stivcen01/NesCat1.0_ESP32/EXAMPLES/_Oscilloscope/oscilloscope_screen.png

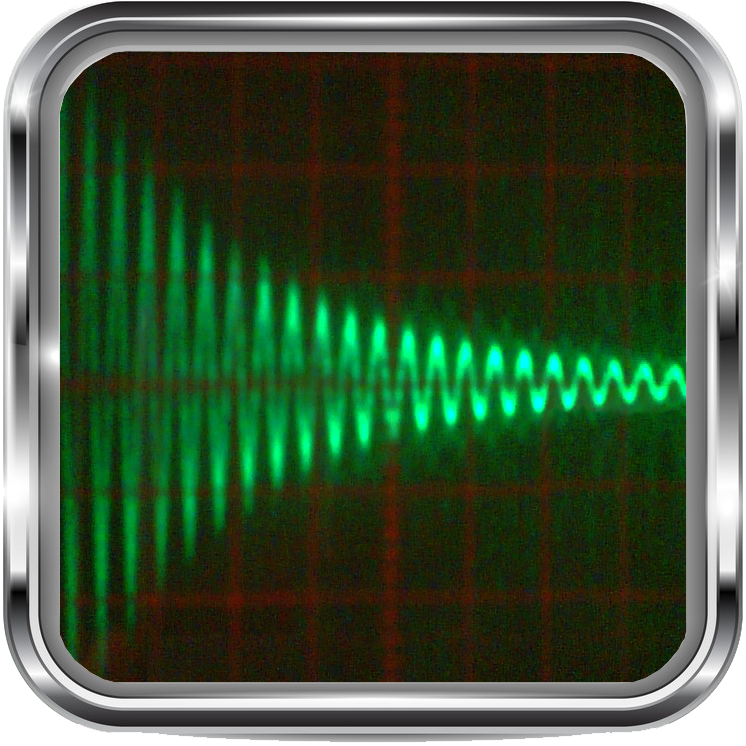
EXAMPLES/_Oscilloscope/oscilloscope_screen.png
