stivcen01/NesCat1.0_ESP32/EXAMPLES/_Player/NCX-PLAYER.png

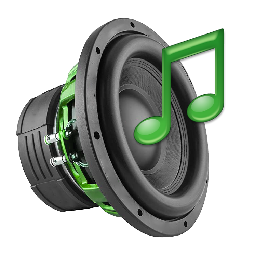
EXAMPLES/_Player/NCX-PLAYER.png
