stivcen01/NesCat1.0_ESP32/HARDWARE/PCB NESCAT 1.0/NESCAT1.0_BRD_TOP.png

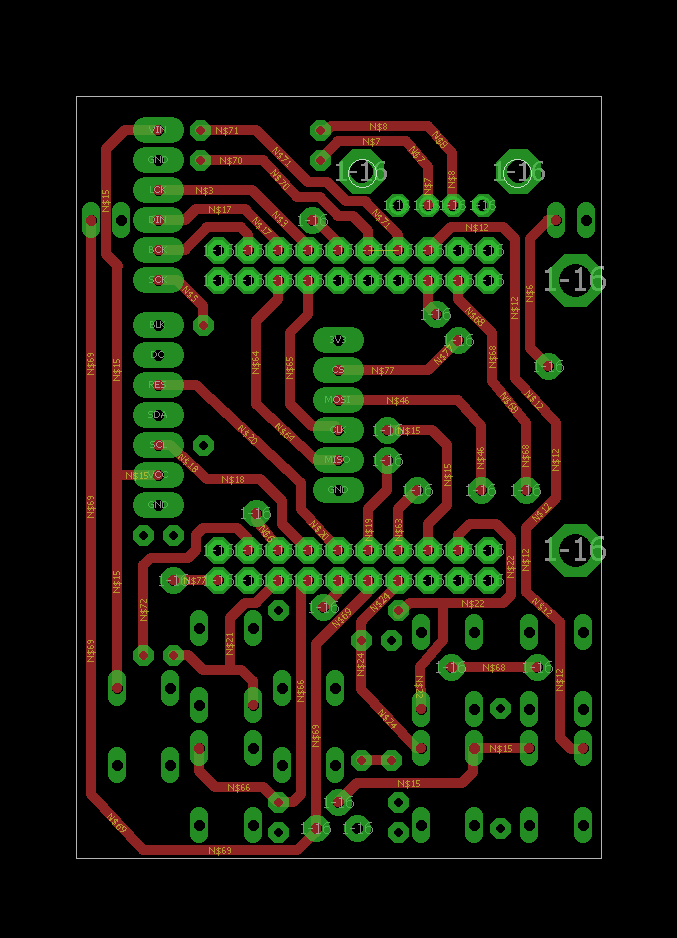
HARDWARE/PCB NESCAT 1.0/NESCAT1.0_BRD_TOP.png
