stivcen01/NesCat1.0_ESP32/RESOURCES/10PCS-LOT-Micro-SD-Storage-Expansion-Board-Mini-Micro-SD-TF-Card-Memory-Shield-Module-With.jpg_Q90.jpg_ (2).jpg

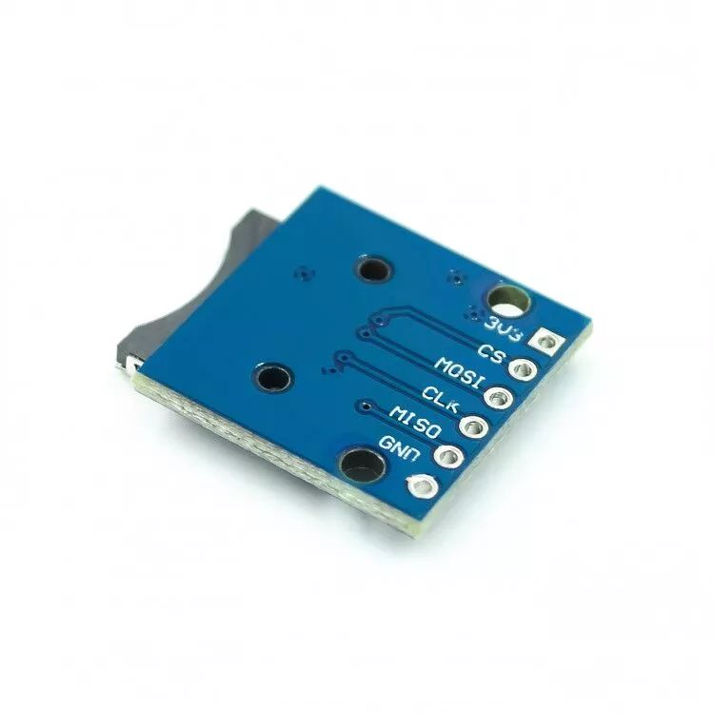
RESOURCES/10PCS-LOT-Micro-SD-Storage-Expansion-Board-Mini-Micro-SD-TF-Card-Memory-Shield-Module-With.jpg_Q90.jpg_ (2).jpg
