stivcen01/NesCat1.0_ESP32/RESOURCES/Interface-I2S-PCM5102A-DAC-Decoder-GY-PCM5102-I2S-Player-Module-For-Raspberry-Pi-pHAT-Format-Board.jpg_Q90.jpg_.jpg

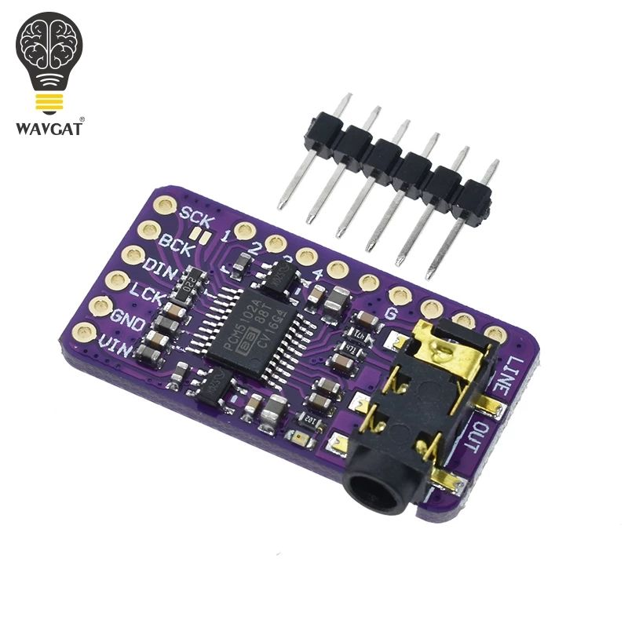
RESOURCES/Interface-I2S-PCM5102A-DAC-Decoder-GY-PCM5102-I2S-Player-Module-For-Raspberry-Pi-pHAT-Format-Board.jpg_Q90.jpg_.jpg
