stivcen01/NesCat1.0_ESP32/oscilloscope.h

#if COMPOSITE_VIDEO_ENABLED

//------------------------
///uint16_t i2s_buff[BUFF_SIZE]; ///using DMA BUFFER 50*1000 samples
uint8_t digital_wave_option = 0; //0-auto | 1-analog | 2-digital data (SERIAL/SPI/I2C/etc)
//------------------------
float v_offset = 0; /// vertical offset is zero in VOLTS
float v_div = 412.5;  ///0.825V/div 4divs!!! -> converted to 8divs (0.412.5V/div)
float v_scale = 0.833333333; //scale 83.3333% verticaly
float h_scale = 0.833333333; //scale 83.3333% horizontaly

uint32_t TIMEBASE = 2; /// 2us or more
//--------------------------------------------------------------------------------
//********************************************************************************
//*  OSCILLOSCOPE FUNCTIONS:                                                     *
//********************************************************************************
class mean_filter {
  public:
    mean_filter(int values) {
      _values = values;
    }

    void init(float value) {
      for (int i = 0; i < _values; i++) {
        _data[i] = value;
      }
    }
    float filter(float reading) {
      float temp = 0;
      _data[_values - 1] = reading;
      for (int i = 0; i < _values - 1; i++) {
        temp += _data[i];
        _data[i] = _data[i + 1];
      }
      temp += reading;
      return temp / float(_values);
    }
    int _values = 5;
    float _data[100] = {0};
};
//--------------------------------------------------------------------------------
float to_scale(float reading) {
  float temp = ///reading-24576;
    TFT_HEIGHT -
    (
      (
        (
          (float)((reading - 24576.0) / 4095.0)
          + (float)(v_offset / 3.3) /// vertical offset is zero in VOLTS
        ) * 3300 /
        (float)(v_div * 8) /// vertically 8divs
      )
    ) * (TFT_HEIGHT - 1) - 1;
  temp = temp * (float)(v_scale); ///vertical scale to %
  temp = temp + (float)(TFT_HEIGHT * ((1 - v_scale) / 2)); // vertical offset from scale/2 %
  return temp;
}
//--------------------------------------------------------------------------------
float to_voltage(float reading) {
  return  (reading - 24576.0) / 4095.0 * 3.3;
}
//--------------------------------------------------------------------------------
//********************************************************************************
void draw_grid() {
  float px_v_per_div = (float)( TFT_HEIGHT * (float)(v_scale)) / 8;
  float px_v_offset = (float)(TFT_HEIGHT * ((1 - v_scale) / 2)); // vertical offset from scale/2 %
  float px_h_per_div = (float)( TFT_WIDTH * (float)(h_scale)) / 8;
  float px_h_offset = (float)(TFT_WIDTH * ((1 - h_scale) / 2)); // vertical offset from scale/2 %

  for (int y = 0; y <= 8; y++) { // 8 divs
    for (int x = 0; x <= 8; x++) { // 8 divs
      //horizontal lines
      if (x < 8)
        for (int i = 0; i < px_h_per_div; i++)  {
          if (i % 8 == 0) screenmemory_drawpixel(x * px_h_per_div + i + px_v_offset, y * px_v_per_div +  px_h_offset , 0x30);
        }
      if (y < 8)
        //vertical lines
        for (int j = 0; j < px_v_per_div; j++)  {
          if (j % 8 == 0) screenmemory_drawpixel(x * px_h_per_div + px_v_offset, y * px_v_per_div + j +  px_h_offset  , 0x30);
        }
    }
  }

  //draw horizontal center line:
  screenmemory_line(px_h_offset , TFT_HEIGHT / 2, TFT_WIDTH - px_h_offset, TFT_HEIGHT / 2, 0x30);

  //draw vertical center line:
  screenmemory_line(TFT_WIDTH / 2 , px_v_offset, TFT_WIDTH / 2, TFT_HEIGHT - px_v_offset, 0x30);
}
//--------------------------------------------------------------------------------
//--------------------------------------------------------------------------------
void peak_mean(uint32_t len, float * max_value, float * min_value, float *pt_mean) {
  max_value[0] = (uint16_t)dma_buff[0][0];
  min_value[0] = (uint16_t)dma_buff[0][0];
  mean_filter filter(5);
  filter.init(dma_buff[0][0]);

  float mean = 0;
  for (uint32_t i = 1; i < len; i++) {
    float value = filter.filter((float)((uint16_t)dma_buff[i / NUM_SAMPLES][i % NUM_SAMPLES]));

    if (value == 0) continue; ///Fix zero values

    if (value > max_value[0]) max_value[0] = value;
    if (value < min_value[0]) min_value[0] = value;

    mean += (uint16_t)dma_buff[i / NUM_SAMPLES][i % NUM_SAMPLES];
  }
  mean /= float(BUFF_SIZE);
  mean = to_voltage(mean);
  pt_mean[0] = mean;
}
//--------------------------------------------------------------------------------
//true if digital/ false if analog
bool digital_analog(uint32_t max_v, uint32_t min_v) {
  uint32_t upper_threshold = max_v - 0.05 * (max_v - min_v);
  uint32_t lower_threshold = min_v + 0.05 * (max_v - min_v);
  uint32_t digital_data = 0;
  uint32_t analog_data = 0;
  for (uint32_t i = 0; i < BUFF_SIZE; i++) {
    if (dma_buff[i / NUM_SAMPLES][i % NUM_SAMPLES] > lower_threshold) {
      if (dma_buff[i / NUM_SAMPLES][i % NUM_SAMPLES] > upper_threshold) {
        //HIGH DIGITAL
        digital_data++;
      } else {
        //ANALOG/TRANSITION
        analog_data++;
      }
    } else {
      //LOW DIGITAL
      digital_data++;
    }
  }
  //more than 50% of data is analog
  if (analog_data < digital_data) return true;
  return false;
}
//--------------------------------------------------------------------------------
void trigger_freq_analog(float sample_rate,
                         float mean,
                         uint32_t max_v,
                         uint32_t min_v,
                         float *pt_freq,
                         float *pt_period,
                         uint32_t *pt_trigger0,
                         uint32_t *pt_trigger1) {
  float freq = 0;
  float period = 0;
  bool signal_side = false;
  uint32_t trigger_count = 0;
  uint32_t trigger_num = 10;
  uint32_t trigger_temp[trigger_num] = {0};
  uint32_t trigger_index = 0;

  //get initial signal relative to the mean
  if (to_voltage(dma_buff[0][0]) > mean) {
    signal_side = true;
  }

  //waveform repetitions calculation + get triggers time
  uint32_t wave_center = (max_v + min_v) / 2;
  for (uint32_t i = 1 ; i < BUFF_SIZE; i++) {
    if (signal_side && dma_buff[i / NUM_SAMPLES][i % NUM_SAMPLES] < wave_center - (wave_center - min_v) * 0.2) {
      signal_side = false;
    } else if (!signal_side && dma_buff[i / NUM_SAMPLES][i % NUM_SAMPLES] > wave_center + (max_v - wave_center) * 0.2) {
      freq++;
      if (trigger_count < trigger_num) {
        trigger_temp[trigger_count] = i;
        trigger_count++;
      }
      signal_side = true;
    }
  }
  //frequency calculation
  if (trigger_count < 2) {
    trigger_temp[0] = 0;
    trigger_index = 0;
    freq = 0;
    period = 0;
  } else {
    //simple frequency calculation fair enough for frequencies over 2khz (20hz resolution)
    freq = freq * NUM_SAMPLES / 50;
    period = (float)(sample_rate * 1000.0) / freq; //us

    //from 2000 to 80 hz -> uses mean of the periods for precision
    /*
          if (freq < 2000 && freq > 80) {
             period = 0;
             for (uint32_t i = 1; i < trigger_count; i++) {
                period += trigger_temp[i] - trigger_temp[i - 1];
             }
             period /= (trigger_count - 1);
             freq = sample_rate * 1000 / period;
          }

          //under 80hz, single period for frequency calculation
          else if (trigger_count > 1 && freq <= 80) {
             period = trigger_temp[1] - trigger_temp[0];
             freq = sample_rate * 1000 / period;
          }
    */
  }

  //setting triggers offset and getting second trigger for debug cursor on drawn_channel1

  ///The trigger function uses a rise porcentage (5%) obove the mean, thus,
  ///the real waveform starting point is some datapoints back.
  ///The resulting trigger gets a negative offset of 5% of the calculated period

  uint32_t trigger2 = 0;
  if (trigger_temp[0] - period * 0.05 > 0 && trigger_count > 1) {
    trigger_index = trigger_temp[0] - period * 0.05;
    trigger2 = trigger_temp[1] - period * 0.05;
  } else if (trigger_count > 2) {
    trigger_index = trigger_temp[1] - period * 0.05;
    if (trigger_count > 2) trigger2 = trigger_temp[2] - period * 0.05;
  }

  pt_trigger0[0] = trigger_index;
  pt_trigger1[0] = trigger2;
  pt_freq[0] = freq;
  pt_period[0] = period;
}
//--------------------------------------------------------------------------------
void trigger_freq_digital(float sample_rate,
                          float mean,
                          uint32_t max_v,
                          uint32_t min_v,
                          float *pt_freq,
                          float *pt_period,
                          uint32_t *pt_trigger0) {

  float freq = 0;
  float period = 0;
  bool signal_side = false;
  uint32_t trigger_count = 0;
  uint32_t trigger_num = 10;
  uint32_t trigger_temp[trigger_num] = {0};
  uint32_t trigger_index = 0;

  //get initial signal relative to the mean
  if (to_voltage(dma_buff[0][0]) > mean) {
    signal_side = true;
  }

  //waveform repetitions calculation + get triggers time
  uint32_t wave_center = (max_v + min_v) / 2;
  bool normal_high = (mean > to_voltage(wave_center)) ? true : false;
  if (max_v - min_v > 4095 * (0.4 / 3.3)) {
    for (uint32_t i = 1 ; i < BUFF_SIZE; i++) {
      if (signal_side && dma_buff[i / NUM_SAMPLES][i % NUM_SAMPLES] < wave_center - (wave_center - min_v) * 0.2) {
        //signal was high, fell -> trigger if normal high
        if (trigger_count < trigger_num && normal_high) {
          trigger_temp[trigger_count] = i;
          trigger_count++;
        }
        signal_side = false;
      } else if (!signal_side && dma_buff[i / NUM_SAMPLES][i % NUM_SAMPLES] > wave_center + (max_v - wave_center) * 0.2) {
        freq++;
        //signal was low, rose -> trigger if normal low
        if (trigger_count < trigger_num && !normal_high) {
          trigger_temp[trigger_count] = i;
          trigger_count++;
        }
        signal_side = true;
      }
    }

    //Digital frequency calculation:
    freq = 281.7133902265831 * freq;
    period = ((float)(sample_rate * 1000.0) / freq) / (28.636 / 2); //us

    if (trigger_count > 1) {
      //from 2000 to 80 hz -> uses mean of the periods for precision
      if (freq < 2000 && freq > 80) {
        period = 0;
        for (uint32_t i = 1; i < trigger_count; i++) {
          period += trigger_temp[i] - trigger_temp[i - 1];
        }
        period /= (trigger_count - 1);
        freq = sample_rate * (NUM_SAMPLES) / period;
      }
      //under 80hz, single period for frequency calculation
      else if (trigger_count > 1 && freq <= 80) {
        period = trigger_temp[1] - trigger_temp[0];
        freq = sample_rate * (2800 / 2) / period;
      }
    }
    trigger_index = trigger_temp[0];

    if (trigger_index > 10) trigger_index -= 10;
    else trigger_index = 0;
  }
  pt_trigger0[0] = trigger_index;
  pt_freq[0] = freq;
  pt_period[0] = period;
}
//********************************************************************************

int shift = 125; //info text shift X
bool info = true;

bool ADC_EXIT = false;
uint8_t spritecolor = 26;

bool timebase_switched=false;


//===============================================================================
void REINIT_ADC(){
  
      // Switch on Slave mode.
      // I2S_CONF_REG -> I2S_RX_SLAVE_MOD
      // Set to 1 to enable slave mode.
      I2S0.conf.rx_slave_mod = 0; //not 1 !!!


      // Enable parallel mode
      // I2S_CONF2_REG -> I2S_LCD_END
      // Set to 1 to enable LCD mode.
      I2S0.conf2.lcd_en = 1;

      // Use HSYNC/VSYNC/HREF to control sampling
      // I2S_CONF2_REG -> I2S_CAMERA_EN
      // Set to 1 to enable camera mode.
      /// I2S0.conf2.camera_en = 1;


      // Configure clock divider
      I2S0.clkm_conf.clkm_div_a   = 1;
      I2S0.clkm_conf.clkm_div_b   = 0;
      I2S0.clkm_conf.clkm_div_num = 1;

      // I2S_FIFO_CONF_REG -> I2S_DSCR_EN
      // FIFO will sink data to DMA
      I2S0.fifo_conf.dscr_en = 1;

      // FIFO configuration
      // I2S_FIFO_CONF_REG -> RX_FIFO_MOD
      I2S0.fifo_conf.rx_fifo_mod          = 1; // 0-3???

      // I2S_FIFO_CONF_REG -> RX_FIFO_MOD_FORCE_EN
      I2S0.fifo_conf.rx_fifo_mod_force_en = 1;

      // I2S_CONF_CHAN_REG -> I2S_RX_CHAN_MOD
      I2S0.conf_chan.rx_chan_mod          = 1;

      // Clear flags which are used in I2S serial mode
      // I2S_SAMPLE_RATE_CONF_REG -> I2S_RX_BITS_MOD
      I2S0.sample_rate_conf.rx_bits_mod = 0;

      // I2S_CONF_REG -> I2S_RX_RIGHT_FIRST
      I2S0.conf.rx_right_first = 0;
      //I2S0.conf.rx_right_first = 0;

      // I2S_CONF_REG -> I2S_RX_MSB_RIGHT
      I2S0.conf.rx_msb_right   = 0;
      //I2S0.conf.rx_msb_right   = 1;

      // I2S_CONF_REG -> I2S_RX_MSB_SHIFT
      I2S0.conf.rx_msb_shift   = 0;
      //I2S0.conf.rx_msb_shift   = 1;

      // I2S_CONF_REG -> I2S_RX_MSB_MONO
      I2S0.conf.rx_mono        = 1;

      // I2S_CONF_REG -> I2S_RX_SHORT_SYNC
      I2S0.conf.rx_short_sync  = 0;

      I2S0.timing.val          = 0;

      for (uint32_t buff_idx = 0; buff_idx < 50; buff_idx++) {
        dma_descriptor[buff_idx].length = 0; //number of byte written to the buffer
        ///    dma_descriptor[buff_idx].size = sizeof(dma_buff[buff_idx]); //max size of the buffer in bytes
        dma_descriptor[buff_idx].size = 2000;  //max size of the buffer in bytes
        dma_descriptor[buff_idx].owner = 1;
        dma_descriptor[buff_idx].sosf = 1;
        dma_descriptor[buff_idx].buf = (uint8_t*)&dma_buff[buff_idx][0];
        dma_descriptor[buff_idx].offset = 0;
        dma_descriptor[buff_idx].empty = 0;
        dma_descriptor[buff_idx].eof = 1;
        //pointer to the next descriptor
        if (buff_idx == 49) dma_descriptor[buff_idx].qe.stqe_next = &dma_descriptor[0];
        else dma_descriptor[buff_idx].qe.stqe_next = &dma_descriptor[buff_idx + 1];
      }
      I2S0.in_link.addr = (uint32_t)&dma_descriptor[0];

      ///Serial.println(dma_descriptor[1].buf[0]);

      // I2S_RX_EOF_NUM_REG
      /// I2S0.rx_eof_num   = sample_count;
      I2S0.rx_eof_num   = 2000 * 50;

      // I2S_IN_LINK_REG -> I2S_INLINK_ADDR
      /// I2S0.in_link.addr = (uint32_t) pFirst;

      // I2S_IN_LINK_REG -> I2S_INLINK_START
      I2S0.in_link.start   = 1;

      // toto sposobuje skakanie obrazu:
      /*  I2S0.int_clr.val   = I2S0.int_raw.val;
        I2S0.int_ena.val   = 0;
        I2S0.int_ena.in_done = 1;
      */
//===============================================================================
}      
//********************************************************************************
//*  ADC TASK:                                                                   *
//********************************************************************************
void core1_task( void * pvParameters ) {
  (void) pvParameters;
  for (;;) {

    float mean = 0;
    float max_v, min_v;
    float freq = 0;
    float period = 0;
    uint32_t trigger0 = 0;
    uint32_t trigger1 = 0;

    float sample_rate = 28636 / 2; // 28.636/2 Mhz

//--------------------------------------------------------------------------------
    //buttons read
    uint32_t lastmtime = millis();
    uint32_t offsetmtime = 250;

    if (TIMEBASE > 1000) offsetmtime = 1000; //1000ms delay
    else offsetmtime = 250; //250ms delay

    while (lastmtime + offsetmtime > millis()) {
      vTaskDelay(pdMS_TO_TICKS(1)); ///1ms delay

      if (digitalRead(PIN_A) == 1) {
        JOY_CROSS = 1;  //A
      }
      if (digitalRead(PIN_B) == 1) {
        JOY_SQUARE = 1;   //B
      }
      if (digitalRead(PIN_SELECT) == 1) {
        JOY_OPTIONS = 1;   //SELECT
      }
      if (digitalRead(PIN_START) == 1) {
        JOY_SHARE = 1;   //START
      }
      if (digitalRead(PIN_UP) == 1) {
        JOY_UP = 1;
      }
      if (digitalRead(PIN_DOWN) == 1) {
        JOY_DOWN = 1;   //DOWN
      }
      if (digitalRead(PIN_LEFT) == 1) {
        JOY_LEFT = 1;   //LEFT
      }
      if (digitalRead(PIN_RIGHT) == 1) {
        JOY_RIGHT = 1;   //RIGHT
      }
    }
//--------------------------------------------------------------------------------

    I2S0.conf.rx_start = 0; /// stop DMA ADC

//--------------------------------------------------------------------------------
    if (JOY_SHARE == 1 && JOY_OPTIONS == 1) { //EXIT
      JOY_SHARE = 0;
      JOY_OPTIONS = 0;
      EXIT = true;
      delay(250);
    }
    if (JOY_CROSS == 1) {  /// PAUSE
      delay(250);
      while (JOY_CROSS == 1) {
        if (digitalRead(PIN_A) == 1) {
          JOY_CROSS = 0;
        }
        delay(10);
      }
    }
    if (JOY_SHARE == 1) {
      if (spritecolor == 26) spritecolor = 6; //green to red
      else if (spritecolor == 6) spritecolor = 1; //red to blue
      else if (spritecolor == 1) spritecolor = 40; //blue to yellow
      else if (spritecolor == 40) spritecolor = 26; //yellow to green
      else spritecolor = 6;
      JOY_SHARE = 0;
    }
    if (JOY_SQUARE == 1) { /// SHOW/HIDE info
      if (digital_wave_option == 0) digital_wave_option = 1;
      else if (digital_wave_option == 1) digital_wave_option = 2;
      else if (digital_wave_option == 2) digital_wave_option = 0;
      else digital_wave_option = 0;
      JOY_SQUARE = 0;
    }
    if (JOY_OPTIONS == 1) { /// SHOW/HIDE info
      if (info == true) info = false;
      else info = true;
      JOY_OPTIONS = 0;
    }
    if (JOY_LEFT == 1) {
      switch (TIMEBASE) {
        case 10000:
          TIMEBASE = 5000;
          break;
        case 5000:
          TIMEBASE = 2000;
          break;
        case 2000:
          TIMEBASE = 1000;
          break;
        case 1000:
          TIMEBASE = 500;
          break;
        case 500:
          TIMEBASE = 200;
          break;
        case 200:
          TIMEBASE = 100;
          break;
        case 100:
          TIMEBASE = 50;
          break;
        case 50:
          TIMEBASE = 20;
          break;
        case 20:
          TIMEBASE = 10;
          break;
        case 10:
          TIMEBASE = 5;
          break;
        case 5:
          TIMEBASE = 2;
          break;
        case 2:
          TIMEBASE = 2; //minimum us/div
          break;
        default:
          TIMEBASE = 10000;
      }
      JOY_LEFT = 0;
      timebase_switched=true;
    }
    if (JOY_RIGHT == 1) {
      switch (TIMEBASE) {
        case 2:
          TIMEBASE = 5;
          break;
        case 5:
          TIMEBASE = 10;
          break;
        case 10:
          TIMEBASE = 20;
          break;
        case 20:
          TIMEBASE = 50;
          break;
        case 50:
          TIMEBASE = 100;
          break;
        case 100:
          TIMEBASE = 200;
          break;
        case 200:
          TIMEBASE = 500;
          break;
        case 500:
          TIMEBASE = 1000;
          break;
        case 1000:
          ///TIMEBASE = 2000;
          TIMEBASE = 1000; //stop here (disabled more than 1ms )
          break;
        case 2000:
          TIMEBASE = 5000;
          break;
        case 5000:
          TIMEBASE = 10000;
          break;
        case 10000:
          TIMEBASE = 10000; //maximum us/div
          break;
        default:
          TIMEBASE = 2;
      }
      JOY_RIGHT = 0;
      timebase_switched=true;
    }


//--------------------------------------------------------------------------------

    peak_mean(BUFF_SIZE, &max_v, &min_v, &mean);

//--------------------------------------------------------------------------------
    //if analog mode OR auto mode and wave recognized as analog

    bool digital_data = false;
    if (digital_wave_option == 1) {
      trigger_freq_analog(sample_rate, mean, max_v, min_v, &freq, &period, &trigger0, &trigger1);
    }  else if (digital_wave_option == 0) {
      digital_data = digital_analog(max_v, min_v);
      if (!digital_data) {
        trigger_freq_analog(sample_rate, mean, max_v, min_v, &freq, &period, &trigger0, &trigger1);
      } else {
        trigger_freq_digital(sample_rate, mean, max_v, min_v, &freq, &period, &trigger0);
      }
    } else {
      trigger_freq_digital(sample_rate, mean, max_v, min_v, &freq, &period, &trigger0);
    }
//--------------------------------------------------------------------------------
    //Clear Screen
    screenmemory_fillscreen(0x3f);

    //Draw Grid
    draw_grid();
//--------------------------------------------------------------------------------
    //DEBUG DATA

    if (DEBUG) {
      Serial.print("digital=1_analog=0: ");
      Serial.println(digital_analog(max_v, min_v));

      Serial.print("mean:");
      Serial.println(mean);
      Serial.print("max_v:");
      Serial.println(max_v);
      Serial.print("min_v:");
      Serial.println(min_v);
      Serial.print("freq:");
      Serial.println(freq);
      Serial.print("period:");
      Serial.println(period);
      Serial.print("trigger0:");
      Serial.println(trigger0);
    }

//--------------------------------------------------------------------------------
    
    ///adjust TIMEBASE:
    if (timebase_switched==true) {
      I2S0.in_link.start   = 0;

    switch (TIMEBASE) {
      case 2:
        rtc_clk_apll_enable(1, 222, 115, 7,0);   //28,636363636 MHz (doubled)   ///tunned maybe ok
        I2S0.sample_rate_conf.tx_bck_div_num = 2;        
        I2S0.sample_rate_conf.rx_bck_div_num = 2; //2x scale time base
        break;
      case 5:
        rtc_clk_apll_enable(1, 222, 115, 7,0);   //28,636363636 MHz (doubled)   ///tunned maybe ok
        I2S0.sample_rate_conf.tx_bck_div_num = 2;
        I2S0.sample_rate_conf.rx_bck_div_num = 2; //2x scale time base
        break;
      case 10:       
        rtc_clk_apll_enable(1, 70, 151, 4, 1);  //14.3181818182Mhz
        I2S0.sample_rate_conf.tx_bck_div_num = 1;
        I2S0.sample_rate_conf.rx_bck_div_num = 2; //4x scale time base
        break;
      case 20:
        rtc_clk_apll_enable(1, 70, 151, 4, 1);  //14.3181818182Mhz
        I2S0.sample_rate_conf.tx_bck_div_num = 1;
        I2S0.sample_rate_conf.rx_bck_div_num = 2; //4x scale time base
        break;
      case 50:
        rtc_clk_apll_enable(1, 70, 151, 4, 1);  //14.3181818182Mhz
        I2S0.sample_rate_conf.tx_bck_div_num = 1;
        I2S0.sample_rate_conf.rx_bck_div_num = 2; //4x scale time base
        break;
      case 100:
        rtc_clk_apll_enable(1, 70, 151, 4, 1);  //14.3181818182Mhz
        I2S0.sample_rate_conf.tx_bck_div_num = 1;
        I2S0.sample_rate_conf.rx_bck_div_num = 4; //8x scale time base
        break;
      case 200:
        rtc_clk_apll_enable(1, 70, 151, 4, 1);  //14.3181818182Mhz
        I2S0.sample_rate_conf.tx_bck_div_num = 1;
        I2S0.sample_rate_conf.rx_bck_div_num = 4; //8x scale time base
        break;
      case 500:
        rtc_clk_apll_enable(1, 70, 151, 4, 1);  //14.3181818182Mhz
        I2S0.sample_rate_conf.tx_bck_div_num = 1;
        I2S0.sample_rate_conf.rx_bck_div_num = 4; //8x scale time base
        break;
      case 1000:
        rtc_clk_apll_enable(1, 70, 151, 4, 1);  //14.3181818182Mhz
        I2S0.sample_rate_conf.tx_bck_div_num = 1;
        I2S0.sample_rate_conf.rx_bck_div_num = 4; //8x scale time base
        break;
      case 2000:
        rtc_clk_apll_enable(1, 70, 151, 4, 1);  //14.3181818182Mhz
        I2S0.sample_rate_conf.tx_bck_div_num = 1;
        I2S0.sample_rate_conf.rx_bck_div_num = 4; //8x scale time base
        break;
      case 5000:
        rtc_clk_apll_enable(1, 70, 151, 4, 1);  //14.3181818182Mhz
        I2S0.sample_rate_conf.tx_bck_div_num = 1;
        I2S0.sample_rate_conf.rx_bck_div_num = 8; //20x scale time base
        break;
      case 10000:
        rtc_clk_apll_enable(1, 70, 151, 4, 1);  //14.3181818182Mhz
        I2S0.sample_rate_conf.tx_bck_div_num = 1;
        I2S0.sample_rate_conf.rx_bck_div_num = 8; //20x scale time base
        break;
      default:
        rtc_clk_apll_enable(1, 222, 115, 7,0);   //28,636363636 MHz (doubled)   ///tunned maybe ok
        I2S0.sample_rate_conf.tx_bck_div_num = 2;        
        I2S0.sample_rate_conf.rx_bck_div_num = 2; //2x scale time base
    }
    timebase_switched=false;
      if (DEBUG) Serial.println("timebase_switched-------------------------------------");
      I2S0.in_link.start = 1;
    
    }
//--------------------------------------------------------------------------------
///calculate freq:
    switch (TIMEBASE) {
      case 2:
        rtc_clk_apll_enable(1, 222, 115, 7,0);   //28,636363636 MHz (doubled)   ///tunned maybe ok
        break;
      case 5:
        rtc_clk_apll_enable(1, 222, 115, 7,0);   //28,636363636 MHz (doubled)   ///tunned maybe ok
        break;
      case 10:
        if ((digital_wave_option == 0 && digital_data == 0) || (digital_wave_option == 1)) freq = (float)freq * (float)1.4*5; //analog wave
        else freq = (float)freq / (float)(4);
        break;
      case 20:
        if ((digital_wave_option == 0 && digital_data == 0) || (digital_wave_option == 1)) freq = (float)freq * (float)1.4 *5; //analog wave
        else freq = (float)freq / (float)(4);
        break;
      case 50:
        if ((digital_wave_option == 0 && digital_data == 0) || (digital_wave_option == 1)) freq = (float)freq * (float)1.4 *5; //analog wave
        else freq = (float)freq / (float)(4);
        break;
      case 100:
        if ((digital_wave_option == 0 && digital_data == 0) || (digital_wave_option == 1)) freq = (float)freq * (float)1.4 *5 /2; //analog wave
        else freq = (float)freq / (float)(8);
        break;
      case 200:
        if ((digital_wave_option == 0 && digital_data == 0) || (digital_wave_option == 1)) freq = (float)freq * (float)1.4 *5 /2; //analog wave
        else freq = (float)freq / (float)(8);
        break;
      case 500:
        if ((digital_wave_option == 0 && digital_data == 0) || (digital_wave_option == 1)) freq = (float)freq * (float)1.4 *5 /2; //analog wave
        else freq = (float)freq / (float)(8);
        break;
      case 1000:
        if ((digital_wave_option == 0 && digital_data == 0) || (digital_wave_option == 1)) freq = (float)freq * (float)1.4 *5 /2; //analog wave
        else freq = (float)freq / (float)(8);
        break;
      case 2000:
        if ((digital_wave_option == 0 && digital_data == 0) || (digital_wave_option == 1)) freq = (float)freq * (float)1.4 *5 /2; //analog wave
        else freq = (float)freq / (float)(8);
        break;
      case 5000:
        if ((digital_wave_option == 0 && digital_data == 0) || (digital_wave_option == 1)) freq = (float)freq / (float)1.4 *5 /4; //analog wave
        else freq = (float)freq / (float)16;
        break;
      case 10000:
        if ((digital_wave_option == 0 && digital_data == 0) || (digital_wave_option == 1)) freq = (float)freq / (float)1.4 *5 /4; //analog wave
        else freq = (float)freq / (float)16;
        break;
      default:
        I2S0.sample_rate_conf.rx_bck_div_num = 2; //1x scale time base
    }

    
//--------------------------------------------------------------------------------
    //draw sprite:


    float px_h_offset = (float)(TFT_WIDTH * ((1 - h_scale) / 2)); // vertical offset from scale/2 %

    uint16_t n_data = 0, o_data = to_scale(dma_buff[0][0]);

    for (uint32_t i = 1; i < 240; i++) {
      uint32_t index = 0;

      switch (TIMEBASE) {
        case 2:
          index = px_h_offset + trigger0 + (uint32_t)((i + 1) * 1.1135);  ///waveform is triggered.... 2.0us/DIV
          break;
        case 5:
          index = px_h_offset + trigger0 + (uint32_t)((i + 1) * 2.8636);  ///waveform is triggered.... 5.0us/DIV
          break;
        case 10:
          index = px_h_offset + trigger0 + (uint32_t)((i + 1) * 5.7272 / 2);  ///waveform is triggered.... 10.0us/DIV
          break;
        case 20:
          index = px_h_offset + trigger0 + (uint32_t)((i + 1) * 1.1135 * 5);  ///waveform is triggered.... 10x2.0us/DIV
          break;
        case 50:
          index = px_h_offset + trigger0 + (uint32_t)((i + 1) * 2.7920 * 5);  ///waveform is triggered.... 10x5.0us/DIV
          break;
        case 100:
          index = px_h_offset + trigger0 + (uint32_t)((i + 1) * 5.5840 * 2.5);  ///waveform is triggered.... 10x10.0us/DIV
          break;
        case 200:
          index = px_h_offset + trigger0 + (uint32_t)((i + 1) * 11.1680 * 2.5);  ///waveform is triggered.... 2.0us/DIV
          break;
        case 500:
          index = px_h_offset + trigger0 + (uint32_t)((i + 1) * 27.9200 * 2.5);  ///waveform is triggered.... 5.0us/DIV
          break;
        case 1000:
          index = px_h_offset + trigger0 + (uint32_t)((i + 1) * 55.8400 * 2.5);  ///waveform is triggered.... 10.0us/DIV
          break;
        case 2000:
          index = px_h_offset + trigger0 + (uint32_t)((i + 1) * 111.6800 * 2.5);  ///waveform is triggered.... 2.0us/DIV
          break;
        case 5000:
          index = px_h_offset + trigger0 + (uint32_t)((i + 1) * 279.2000 / 2 * 5.0); ///waveform is triggered.... 5.0us/DIV
          break;
        case 10000:
          index = px_h_offset + trigger0 + (uint32_t)((i + 1) * 558.4000 / 2 * 5.0); ///waveform is triggered.... 10.0us/DIV
          break;
        default:
          index = px_h_offset + trigger0 + (uint32_t)((i + 1) * 0.944);  ///waveform is triggered.... 2.0us/DIV
      }
//--------------------------------------------------------------------------------
      if (index < BUFF_SIZE - 240) {
        n_data = to_scale(dma_buff[index / NUM_SAMPLES][index % NUM_SAMPLES]);
        screenmemory_line(i - 1, o_data, i, n_data, spritecolor); //26=green //6=red
        screenmemory_line(i  , o_data + 1, i + 1, n_data - 1, spritecolor); //26=green //6=red ///DOUBLE LINE...
        if (LCD_ENABLED) xQueueSend(vidQueue, &SCREENMEMORY, 0); //refresh LCD
        o_data = n_data;
      }
    }
//--------------------------------------------------------------------------------


//--------------------------------------------------------------------------------
    if (info) {
      screenmemory_drawrectangle(shift + 12, 20, 240 - shift - 20, 36,  0x30);

      set_font_XY(shift + 15, 20 + 5);
      sprintf(textbuf, "P-P:%.3fV", (float)((to_voltage(max_v) - to_voltage(min_v))));
      draw_string(textbuf, 48);

    if (freq < 1000) sprintf(textbuf, "%.3fHz", (float)freq);
    else if (freq < 1000000) sprintf(textbuf, "%.1fkHz", (float)(freq / 1000));
    else sprintf(textbuf, "----");

    //very high frequency on low time base
    if ((TIMEBASE >= 5000 && digital_wave_option == 1 && freq > 200) ||
        (TIMEBASE >= 5000 && digital_wave_option == 0 && digital_data == 0 && freq > 200)) sprintf(textbuf, "----");

    //very low frequency on high time base
    if ((TIMEBASE <= 10 && digital_wave_option == 1 && freq < 2000) ||
        (TIMEBASE <= 10 && digital_wave_option == 0 && digital_data == 0 && freq < 2000)) sprintf(textbuf, "----");
     set_font_XY(shift + 15, 20 + 20);
      draw_string(textbuf, 48);

    if (mean > 1.0) sprintf(textbuf, "Avg:%.2fV", (float)mean);
    else sprintf(textbuf, "Avg:%.2fdmV", (float)(mean * 1000.0));

      if (digital_wave_option == 0 && digital_data == 0) sprintf(textbuf, "AUTO:AN."); //AUTO:ANALOG
      else if (digital_wave_option == 0 && digital_data == 1) sprintf(textbuf, "AUTO:DIG."); //AUTO:DIGITAL
      else if (digital_wave_option == 1) sprintf(textbuf, "ANALOG"); //ANALOG
      else if (digital_wave_option == 2) sprintf(textbuf, "DIGITAL"); //DIGITAL
      else sprintf(textbuf, "UNKNOWN"); //DIGITAL
      set_font_XY(0 + 24, 24);
      draw_string(textbuf, 48);

      if (TIMEBASE < 1000) sprintf(textbuf, "T:%.0fus", (float)(TIMEBASE));
      else if (TIMEBASE < 1000000)  sprintf(textbuf, "T:%.0fms", (float)(TIMEBASE / 1000));
      else  sprintf(textbuf, "T:----us");
      set_font_XY(0 + 24, 256 - 24 - 32);
         draw_string(textbuf, 48);
      }
//--------------------------------------------------------------------------------
      I2S0.conf.rx_start = 1; //start DMA ADC
   }
}
#endif
